dumitrescuoctavian22/1v2-5v_buck/images/3d model/3dMain.PNG

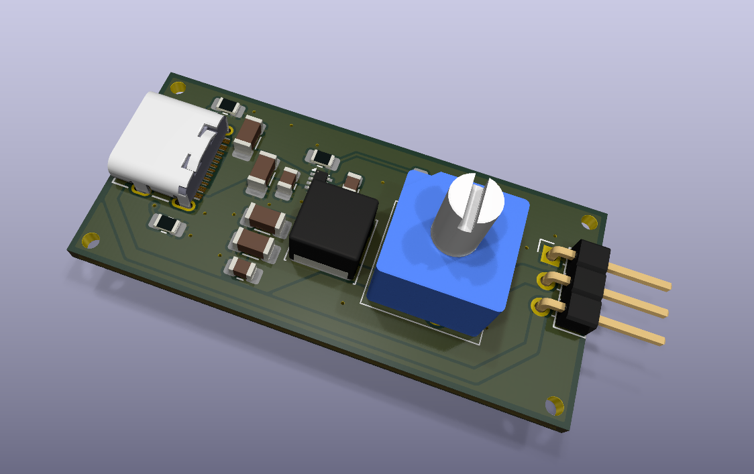
images/3d model/3dMain.PNG
